bluecube/nas-case/spacer.SLDPRT

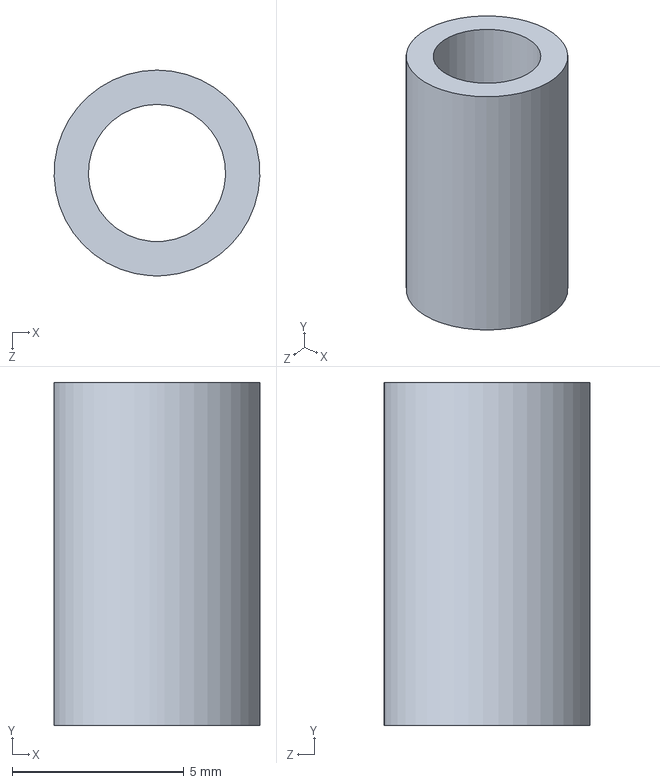
[picture p20: CAD file, 2014-12-26]
spacer.SLDPRT
6.00 x 10.0 x 6.00 mm
