bluecube/nas-case/floor.SLDPRT

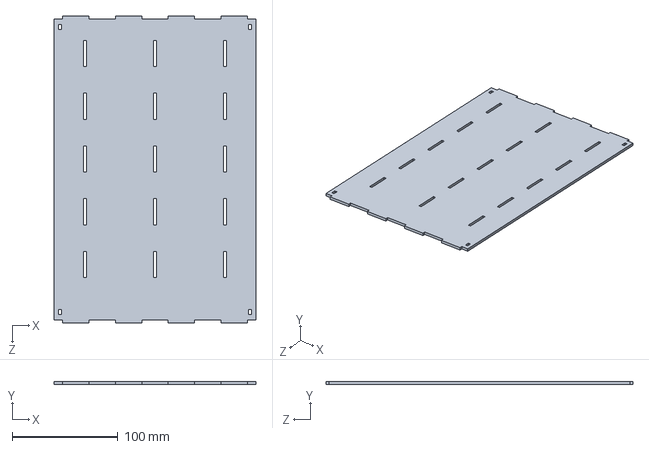
[picture p21: CAD file, 2014-12-26]
floor.SLDPRT
191.0 x 3.00 x 291.0 mm
