bluecube/nas-case/ceiling-bar.SLDPRT

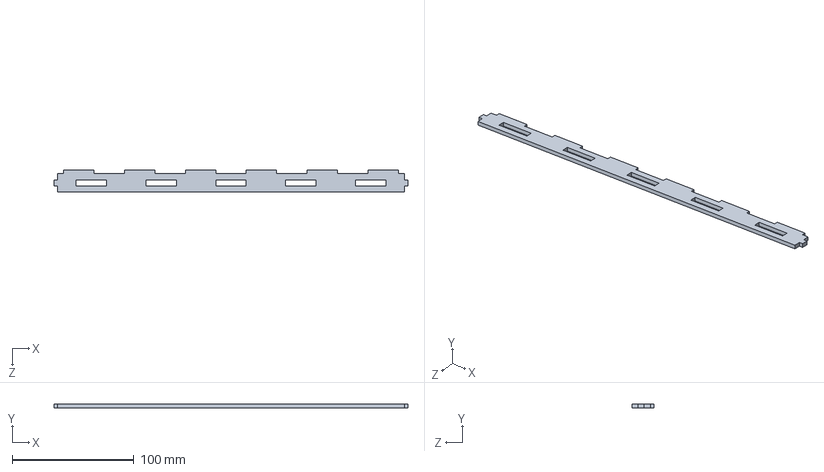
[picture p22: CAD file, 2014-12-26]
ceiling-bar.SLDPRT
291.0 x 3.00 x 18.0 mm
