bluecube/nas-case/120fan.SLDPRT

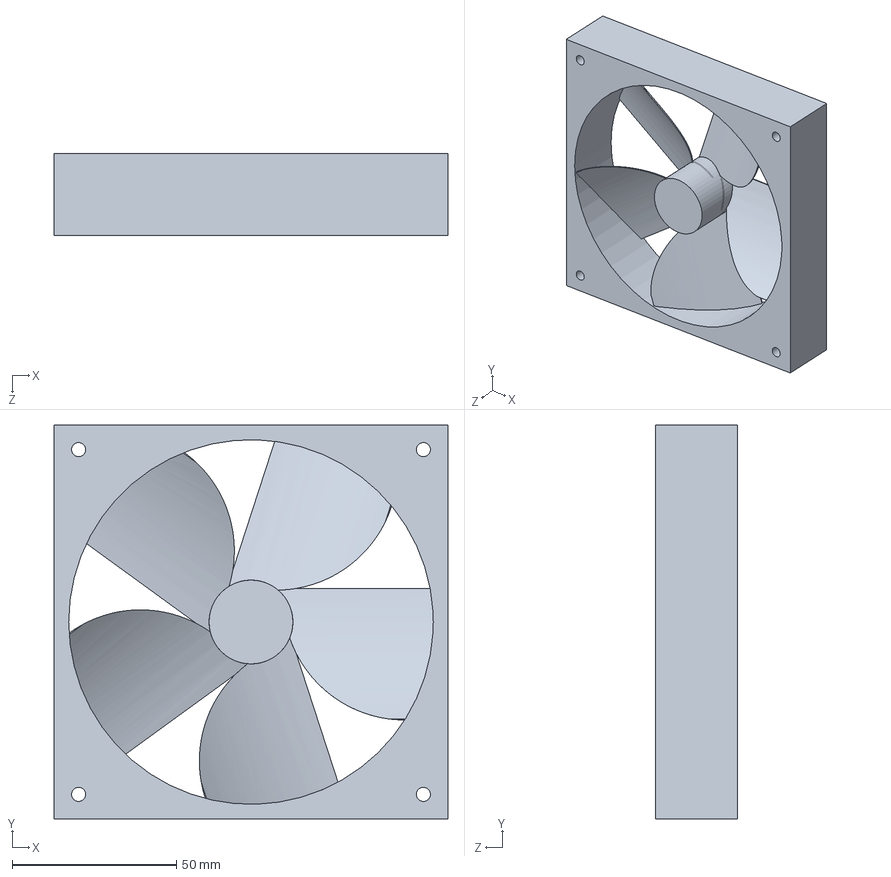
[picture p23: CAD file, 2014-12-26]
120fan.SLDPRT
120.0 x 120.0 x 25.0 mm
