bluecube/nas-case/beam.SLDPRT

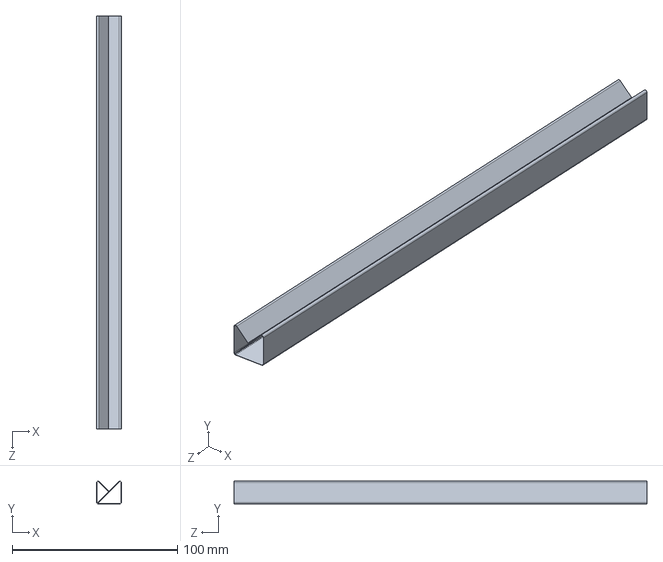
[picture p24: CAD file, 2014-12-26]
beam.SLDPRT
15.0 x 13.8 x 250.0 mm
