bluecube/nas-case/side.SLDPRT

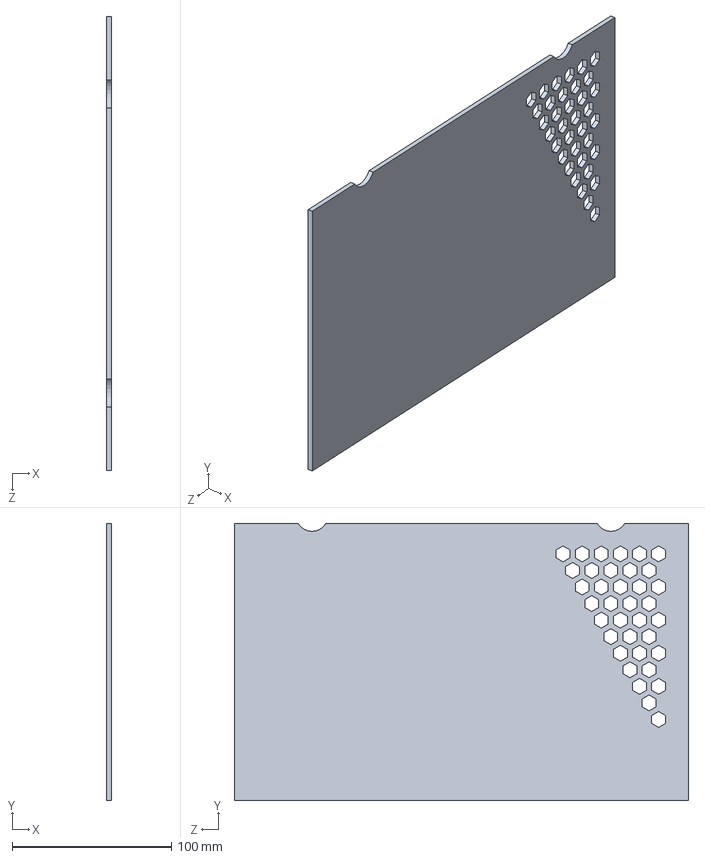
[picture p25: CAD file, 2014-12-26]
side.SLDPRT
3.00 x 174.0 x 285.0 mm
