bluecube/nas-case/magnet.SLDPRT

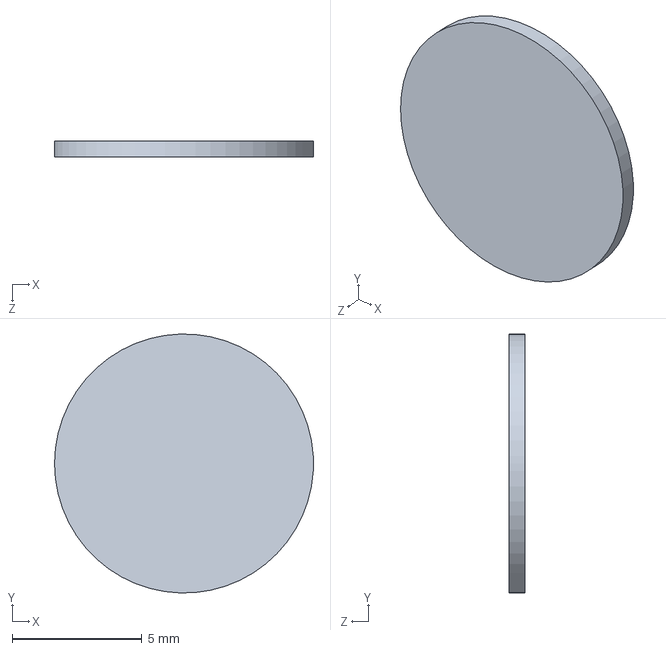
[picture p26: CAD file, 2014-12-26]
magnet.SLDPRT
10.0 x 10.00 x 0.6 mm
