bluecube/nas-case/120fan_cover.SLDPRT

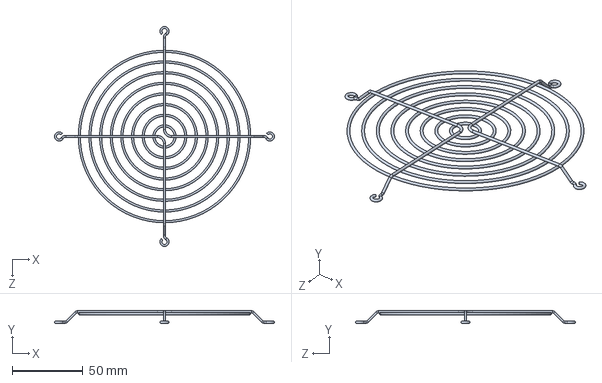
[picture p27: CAD file, 2014-12-26]
120fan_cover.SLDPRT
155.0 x 8.90 x 155.0 mm
